bbenchoff/NextBusPico/Graphics/Transit_Graphics/1.png

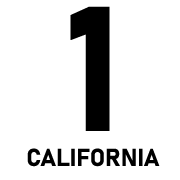
Graphics/Transit_Graphics/1.png
