bbenchoff/NextBusPico/Graphics/Transit_Graphics/1X.png

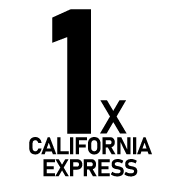
Graphics/Transit_Graphics/1X.png
