bbenchoff/NextBusPico/Graphics/Transit_Graphics/2.png

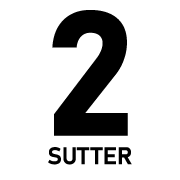
Graphics/Transit_Graphics/2.png
