bbenchoff/NextBusPico/Graphics/Transit_Graphics/5.png

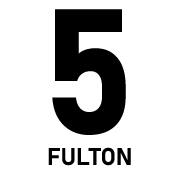
Graphics/Transit_Graphics/5.png
