bbenchoff/NextBusPico/Graphics/Transit_Graphics/5R.png

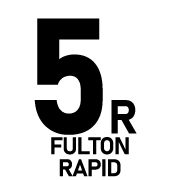
Graphics/Transit_Graphics/5R.png
