bbenchoff/NextBusPico/Graphics/Transit_Graphics/6.png

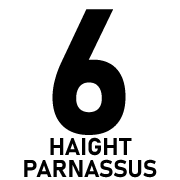
Graphics/Transit_Graphics/6.png
