bbenchoff/NextBusPico/Graphics/Transit_Graphics/7.png

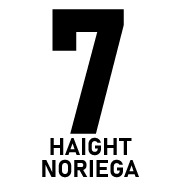
Graphics/Transit_Graphics/7.png
