bbenchoff/NextBusPico/Graphics/Transit_Graphics/8.png

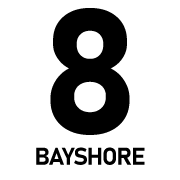
Graphics/Transit_Graphics/8.png
