bbenchoff/NextBusPico/Graphics/Transit_Graphics/8AX.png

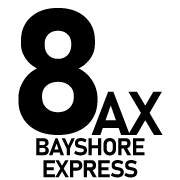
Graphics/Transit_Graphics/8AX.png
