bbenchoff/NextBusPico/Graphics/Transit_Graphics/9.png

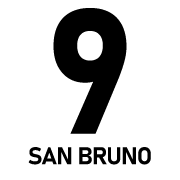
Graphics/Transit_Graphics/9.png
