bbenchoff/NextBusPico/Graphics/Transit_Graphics/9R.png

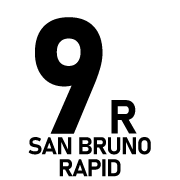
Graphics/Transit_Graphics/9R.png
