bbenchoff/NextBusPico/Graphics/Transit_Graphics/12.png

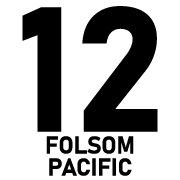
Graphics/Transit_Graphics/12.png
