bbenchoff/NextBusPico/Graphics/Transit_Graphics/14.png

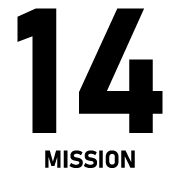
Graphics/Transit_Graphics/14.png
