bbenchoff/NextBusPico/Graphics/Transit_Graphics/14R.png

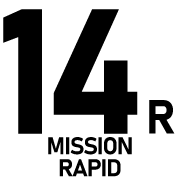
Graphics/Transit_Graphics/14R.png
