bbenchoff/NextBusPico/Graphics/Transit_Graphics/15.png

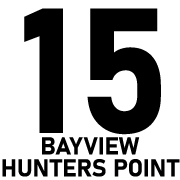
Graphics/Transit_Graphics/15.png
