bbenchoff/NextBusPico/Graphics/Transit_Graphics/18.png

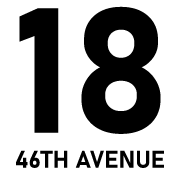
Graphics/Transit_Graphics/18.png
