bbenchoff/NextBusPico/Graphics/Transit_Graphics/19.png

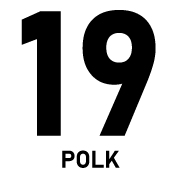
Graphics/Transit_Graphics/19.png
