bbenchoff/NextBusPico/Graphics/Transit_Graphics/21.png

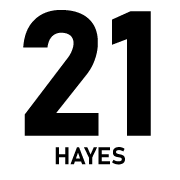
Graphics/Transit_Graphics/21.png
