bbenchoff/NextBusPico/Graphics/Transit_Graphics/22.png

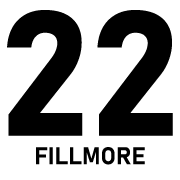
Graphics/Transit_Graphics/22.png
