bbenchoff/NextBusPico/Graphics/Transit_Graphics/23.png

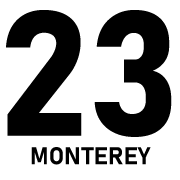
Graphics/Transit_Graphics/23.png
