bbenchoff/NextBusPico/Graphics/Transit_Graphics/24.png

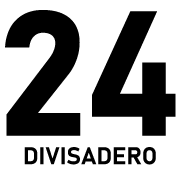
Graphics/Transit_Graphics/24.png
