bbenchoff/NextBusPico/Graphics/Transit_Graphics/25.png

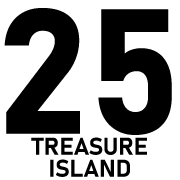
Graphics/Transit_Graphics/25.png
