bbenchoff/NextBusPico/Graphics/Transit_Graphics/27.png

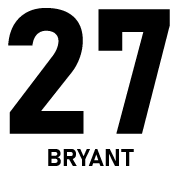
Graphics/Transit_Graphics/27.png
