bbenchoff/NextBusPico/Graphics/Transit_Graphics/28.png

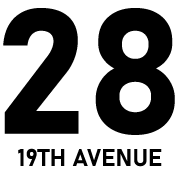
Graphics/Transit_Graphics/28.png
