bbenchoff/NextBusPico/Graphics/Transit_Graphics/28R.png

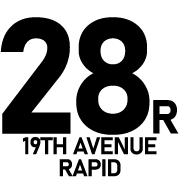
Graphics/Transit_Graphics/28R.png
