bbenchoff/NextBusPico/Graphics/Transit_Graphics/29.png

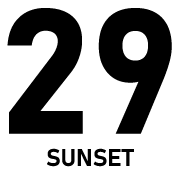
Graphics/Transit_Graphics/29.png
