bbenchoff/NextBusPico/Graphics/Transit_Graphics/30.png

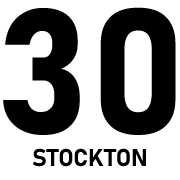
Graphics/Transit_Graphics/30.png
