bbenchoff/NextBusPico/Graphics/Transit_Graphics/31.png

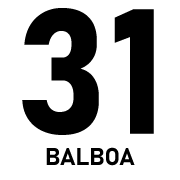
Graphics/Transit_Graphics/31.png
