bbenchoff/NextBusPico/Graphics/Transit_Graphics/33.png

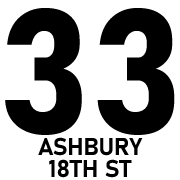
Graphics/Transit_Graphics/33.png
