bbenchoff/NextBusPico/Graphics/Transit_Graphics/35.png

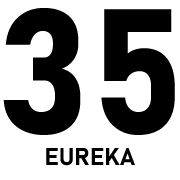
Graphics/Transit_Graphics/35.png
