bbenchoff/NextBusPico/Graphics/Transit_Graphics/36.png

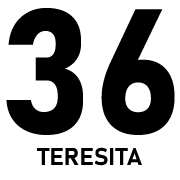
Graphics/Transit_Graphics/36.png
