bbenchoff/NextBusPico/Graphics/Transit_Graphics/37.png

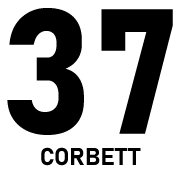
Graphics/Transit_Graphics/37.png
