bbenchoff/NextBusPico/Graphics/Transit_Graphics/38.png

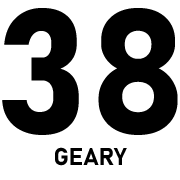
Graphics/Transit_Graphics/38.png
