bbenchoff/NextBusPico/Graphics/Transit_Graphics/38R.png

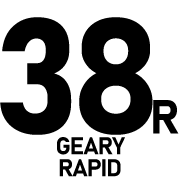
Graphics/Transit_Graphics/38R.png
