bbenchoff/NextBusPico/Graphics/Transit_Graphics/39.png

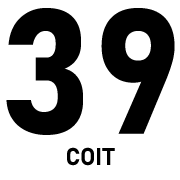
Graphics/Transit_Graphics/39.png
