bbenchoff/NextBusPico/Graphics/Transit_Graphics/39T.png

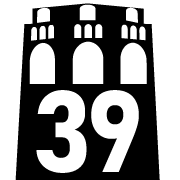
Graphics/Transit_Graphics/39T.png
