bbenchoff/NextBusPico/Graphics/Transit_Graphics/43.png

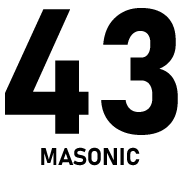
Graphics/Transit_Graphics/43.png
