bbenchoff/NextBusPico/Graphics/Transit_Graphics/44.png

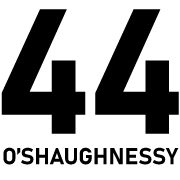
Graphics/Transit_Graphics/44.png
