bbenchoff/NextBusPico/Graphics/Transit_Graphics/45.png

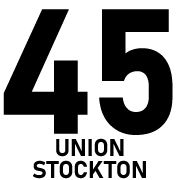
Graphics/Transit_Graphics/45.png
