bbenchoff/NextBusPico/Graphics/Transit_Graphics/48.png

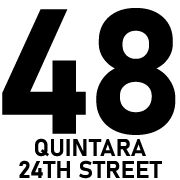
Graphics/Transit_Graphics/48.png
