bbenchoff/NextBusPico/Graphics/Transit_Graphics/49.png

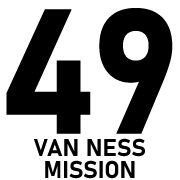
Graphics/Transit_Graphics/49.png
