bbenchoff/NextBusPico/Graphics/Transit_Graphics/52.png

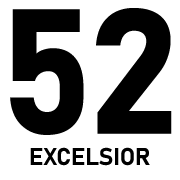
Graphics/Transit_Graphics/52.png
