bbenchoff/NextBusPico/Graphics/Transit_Graphics/54.png

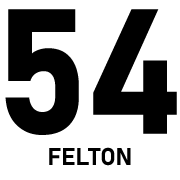
Graphics/Transit_Graphics/54.png
