bbenchoff/NextBusPico/Graphics/Transit_Graphics/55.png

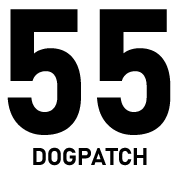
Graphics/Transit_Graphics/55.png
