bbenchoff/NextBusPico/Graphics/Transit_Graphics/56.png

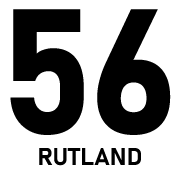
Graphics/Transit_Graphics/56.png
