bbenchoff/NextBusPico/Graphics/Transit_Graphics/57.png

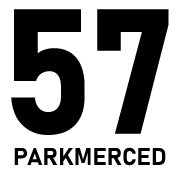
Graphics/Transit_Graphics/57.png
