bbenchoff/NextBusPico/Graphics/Transit_Graphics/58.png

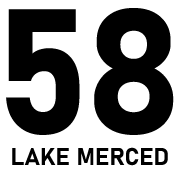
Graphics/Transit_Graphics/58.png
