bbenchoff/NextBusPico/Graphics/Transit_Graphics/66.png

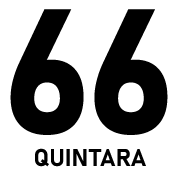
Graphics/Transit_Graphics/66.png
