bbenchoff/NextBusPico/Graphics/Transit_Graphics/67.png

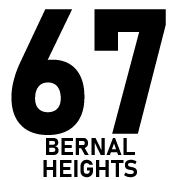
Graphics/Transit_Graphics/67.png
