bbenchoff/NextBusPico/Graphics/Transit_Graphics/90.png

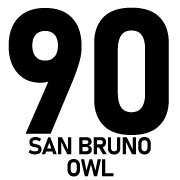
Graphics/Transit_Graphics/90.png
