bbenchoff/NextBusPico/Graphics/Transit_Graphics/91.png

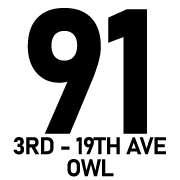
Graphics/Transit_Graphics/91.png
