bbenchoff/NextBusPico/Graphics/Transit_Graphics/714.png

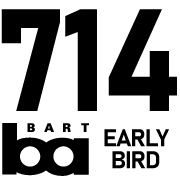
Graphics/Transit_Graphics/714.png
