bbenchoff/NextBusPico/Graphics/Transit_Graphics/arduino_output/2_processed.png

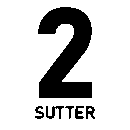
Graphics/Transit_Graphics/arduino_output/2_processed.png
