bbenchoff/NextBusPico/Graphics/Transit_Graphics/arduino_output/8_processed.png

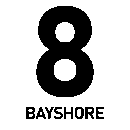
Graphics/Transit_Graphics/arduino_output/8_processed.png
