bbenchoff/NextBusPico/Graphics/Transit_Graphics/arduino_output/8BX_processed.png

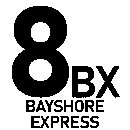
Graphics/Transit_Graphics/arduino_output/8BX_processed.png
