bbenchoff/NextBusPico/Graphics/Transit_Graphics/arduino_output/22_processed.png

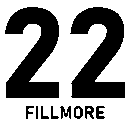
Graphics/Transit_Graphics/arduino_output/22_processed.png
