bbenchoff/NextBusPico/Graphics/Transit_Graphics/arduino_output/36_processed.png

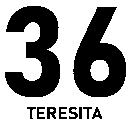
Graphics/Transit_Graphics/arduino_output/36_processed.png
