bbenchoff/NextBusPico/Graphics/Transit_Graphics/arduino_output/CA_processed.png

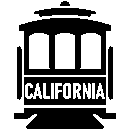
Graphics/Transit_Graphics/arduino_output/CA_processed.png
