bbenchoff/NextBusPico/Graphics/Transit_Graphics/arduino_output/F_processed.png

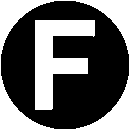
Graphics/Transit_Graphics/arduino_output/F_processed.png
