bbenchoff/NextBusPico/Graphics/Transit_Graphics/arduino_output/J_processed.png

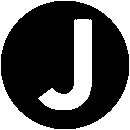
Graphics/Transit_Graphics/arduino_output/J_processed.png
