bbenchoff/NextBusPico/Graphics/Transit_Graphics/arduino_output/K_processed.png

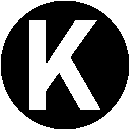
Graphics/Transit_Graphics/arduino_output/K_processed.png
