bbenchoff/NextBusPico/Graphics/Transit_Graphics/arduino_output/KBUS_processed.png

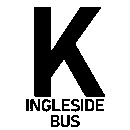
Graphics/Transit_Graphics/arduino_output/KBUS_processed.png
