bbenchoff/NextBusPico/Graphics/Transit_Graphics/arduino_output/M_processed.png

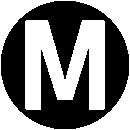
Graphics/Transit_Graphics/arduino_output/M_processed.png
