bbenchoff/NextBusPico/Graphics/Transit_Graphics/arduino_output/N_processed.png

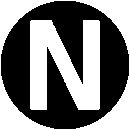
Graphics/Transit_Graphics/arduino_output/N_processed.png
