bbenchoff/NextBusPico/Graphics/Transit_Graphics/arduino_output/PH_processed.png

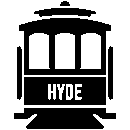
Graphics/Transit_Graphics/arduino_output/PH_processed.png
