bbenchoff/NextBusPico/Graphics/Transit_Graphics/arduino_output/T_processed.png

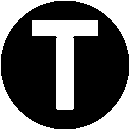
Graphics/Transit_Graphics/arduino_output/T_processed.png
