bbenchoff/NextBusPico/Graphics/Transit_Graphics/arduino_output/TBUS_processed.png

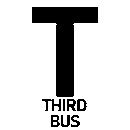
Graphics/Transit_Graphics/arduino_output/TBUS_processed.png
