bbenchoff/NextBusPico/Graphics/Transit_Graphics/KBUS.png

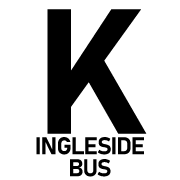
Graphics/Transit_Graphics/KBUS.png
