bbenchoff/NextBusPico/PicoBusses/config.template.h

// WiFi credentials
const char* ssid = "YOUR_WIFI_SSID";
const char* password = "YOUR_WIFI_PASSWORD";

// API key for 511.org
// Sign up at https://511.org/open-data/token
String APIkey = "YOUR_API_KEY";
